danb35/ubg-downloader/Pictures/IMG_0393.jpg

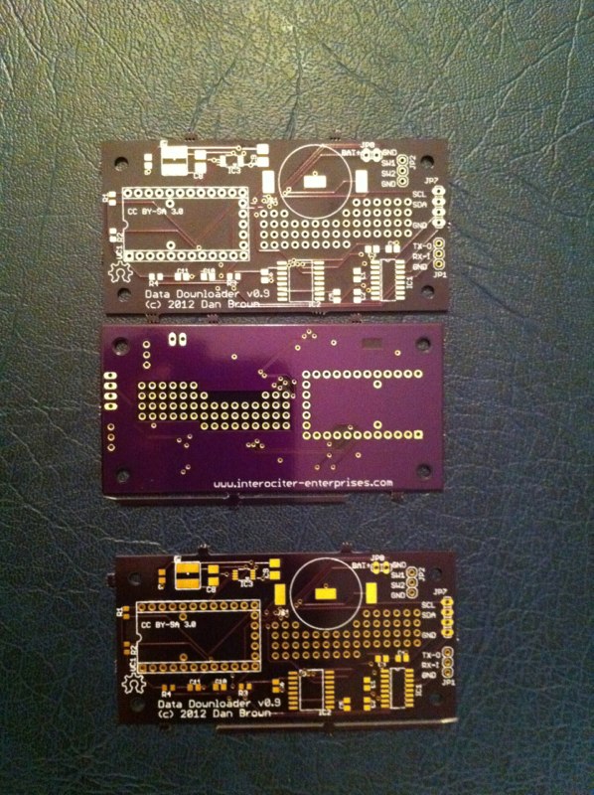
Pictures/IMG_0393.jpg
