danb35/ubg-downloader/Pictures/IMG_0398.jpg

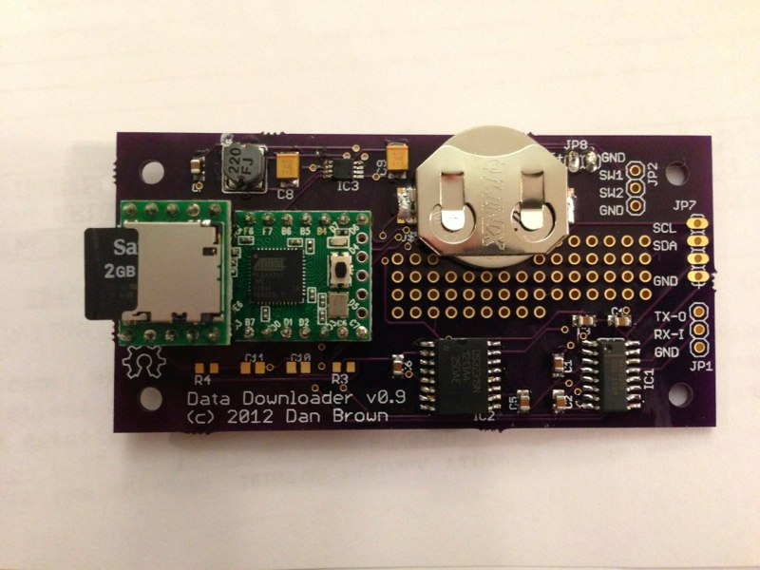
Pictures/IMG_0398.jpg
